jabadiagm/MSXgoauld_tn20k/fpga/OCM_3.9/peripheral/iplrom_304k.vhd

--
-- iplrom_304k.vhd
--   initial program loader for Cyclone & EPCS (Altera)
--   Revision 2.00
--
-- Copyright (c) 2006 Kazuhiro Tsujikawa (ESE Artists' factory)
-- All rights reserved.
--
-- Redistribution and use of this source code or any derivative works, are
-- permitted provided that the following conditions are met:
--
-- 1. Redistributions of source code must retain the above copyright notice,
--    this list of conditions and the following disclaimer.
-- 2. Redistributions in binary form must reproduce the above copyright
--    notice, this list of conditions and the following disclaimer in the
--    documentation and/or other materials provided with the distribution.
-- 3. Redistributions may not be sold, nor may they be used in a commercial
--    product or activity without specific prior written permission.
--
-- THIS SOFTWARE IS PROVIDED BY THE COPYRIGHT HOLDERS AND CONTRIBUTORS
-- "AS IS" AND ANY EXPRESS OR IMPLIED WARRANTIES, INCLUDING, BUT NOT LIMITED
-- TO, THE IMPLIED WARRANTIES OF MERCHANTABILITY AND FITNESS FOR A PARTICULAR
-- PURPOSE ARE DISCLAIMED. IN NO EVENT SHALL THE COPYRIGHT OWNER OR
-- CONTRIBUTORS BE LIABLE FOR ANY DIRECT, INDIRECT, INCIDENTAL, SPECIAL,
-- EXEMPLARY, OR CONSEQUENTIAL DAMAGES (INCLUDING, BUT NOT LIMITED TO,
-- PROCUREMENT OF SUBSTITUTE GOODS OR SERVICES; LOSS OF USE, DATA, OR PROFITS;
-- OR BUSINESS INTERRUPTION) HOWEVER CAUSED AND ON ANY THEORY OF LIABILITY,
-- WHETHER IN CONTRACT, STRICT LIABILITY, OR TORT (INCLUDING NEGLIGENCE OR
-- OTHERWISE) ARISING IN ANY WAY OUT OF THE USE OF THIS SOFTWARE, EVEN IF
-- ADVISED OF THE POSSIBILITY OF SUCH DAMAGE.
--
-- IPL-ROM Revision 2.00 for 304 kB unpacked
-- EPCS4 start adr 34000h - Optimized by KdL 2017.09.18
--

library ieee;
    use ieee.std_logic_1164.all;
    use ieee.std_logic_unsigned.all;

entity iplrom is
    port (
        clk     : in  std_logic;
        adr     : in  std_logic_vector ( 15 downto 0 );
        dbi     : out std_logic_vector (  7 downto 0 )
    );
end iplrom;

architecture rtl of iplrom is
    type rom_type is array ( 0 to 763 + 260 ) of std_logic_vector (  7 downto 0 );
    constant ipl_data : rom_type := (
        X"F3",X"01",X"FC",X"02",X"11",X"00",X"FC",X"63",X"6B",X"ED",X"B0",X"21",X"4C",X"FD",X"01",X"99",
        X"02",X"ED",X"B3",X"01",X"9A",X"20",X"ED",X"BB",X"C3",X"1B",X"FC",X"31",X"FF",X"FF",X"3E",X"D4",
        X"D3",X"40",X"3E",X"80",X"32",X"00",X"70",X"2A",X"00",X"80",X"11",X"41",X"42",X"ED",X"52",X"CA",
        X"1D",X"FD",X"3E",X"40",X"32",X"00",X"60",X"21",X"00",X"C0",X"04",X"4D",X"55",X"5D",

--      X"C3",X"86",X"FC",X"38",X"43",      -- loading BIOS from EPCS only
        X"CD",X"14",X"FE",X"38",X"43",      -- loading BIOS from SD CARD or EPCS (default)
--      X"CD",X"14",X"FE",X"38",X"FB",      -- loading BIOS from SD CARD only

                          X"21",X"00",X"C0",X"01",X"80",X"00",X"3E",X"46",X"ED",X"B1",X"B7",X"20",X"0C",
        X"86",X"23",X"86",X"D6",X"DB",X"2B",X"20",X"F1",X"48",X"59",X"51",X"37",X"38",X"57",X"06",X"04",
        X"21",X"C6",X"C1",X"E5",X"5E",X"23",X"56",X"23",X"4E",X"79",X"B2",X"B3",X"E1",X"20",X"07",X"11",
        X"10",X"00",X"19",X"10",X"EE",X"37",X"38",X"0E",X"D5",X"C5",X"06",X"01",X"21",X"00",X"C0",X"CD",
        X"14",X"FE",X"C1",X"D1",X"30",X"2F",X"21",X"8C",X"FD",X"22",X"7E",X"FD",X"3E",X"60",X"32",X"00",
        X"60",X"11",X"A0",X"01",X"3E",X"80",X"06",X"03",X"CD",X"6C",X"FD",X"06",X"03",X"CD",X"66",X"FD",
        X"CD",X"6C",X"FD",X"CD",X"4F",X"FD",X"06",X"05",X"CD",X"6C",X"FD",X"CD",X"61",X"FD",X"06",X"07",
        X"CD",X"6C",X"FD",X"18",X"66",X"DD",X"21",X"00",X"C0",X"DD",X"6E",X"0E",X"DD",X"66",X"0F",X"79",
        X"19",X"CE",X"00",X"4F",X"DD",X"5E",X"11",X"DD",X"56",X"12",X"7B",X"E6",X"0F",X"06",X"04",X"CB",
        X"3A",X"CB",X"1B",X"10",X"FA",X"B7",X"28",X"01",X"13",X"D5",X"DD",X"46",X"10",X"DD",X"5E",X"16",
        X"DD",X"56",X"17",X"79",X"19",X"CE",X"00",X"10",X"FB",X"D1",X"19",X"EB",X"4F",X"D5",X"C5",X"06",
        X"01",X"21",X"00",X"C0",X"CD",X"14",X"FE",X"38",X"0E",X"2A",X"00",X"C0",X"11",X"41",X"42",X"B7",
        X"ED",X"52",X"C1",X"D1",X"28",X"01",X"37",X"DA",X"86",X"FC",X"3E",X"80",X"06",X"09",X"CD",X"6E",
        X"FD",X"CD",X"4F",X"FD",X"06",

--      X"0F",                              -- loading BIOS 384 kB from SD CARD / JIS1 only
        X"17",                              -- loading BIOS 512 kB from SD CARD / JIS1+JIS2 (default)

                                            X"CD",X"6E",X"FD",X"2F",X"07",X"D3",X"4E",X"AF",X"32",X"00",
        X"60",X"3C",X"32",X"00",X"68",X"32",X"00",X"70",X"32",X"00",X"78",X"3E",X"C0",X"D3",X"A8",X"C7",
        X"77",X"05",X"55",X"02",X"65",X"04",X"11",X"06",X"64",X"06",X"61",X"03",X"73",X"01",X"71",X"06",
        X"27",X"01",X"51",X"03",X"27",X"01",X"17",X"07",X"33",X"06",X"11",X"00",X"00",X"90",X"00",X"08",
        X"3A",X"2D",X"80",X"D6",X"03",X"D3",X"4F",X"D3",X"F4",X"0F",X"F6",X"C9",X"32",X"BB",X"FD",X"08",
        X"C9",X"21",X"18",X"23",X"18",X"03",X"21",X"18",X"25",X"22",X"95",X"FD",X"4B",X"04",X"32",X"00",
        X"70",X"3C",X"32",X"00",X"78",X"3C",X"F5",X"C5",X"06",X"20",X"21",X"00",X"80",X"CD",X"14",X"FE",
        X"C1",X"E1",X"D8",X"7C",X"10",X"E8",X"60",X"68",X"22",X"95",X"FD",X"C9",X"D5",X"C5",X"CB",X"23",
        X"CB",X"12",X"48",X"AF",X"47",X"00",X"00",X"E5",X"21",X"00",X"40",X"36",X"03",X"72",X"73",X"70",
        X"7E",X"D1",X"7E",X"12",X"13",X"7E",X"12",X"13",X"10",X"F8",X"0D",X"20",X"F5",X"3A",X"00",X"50",
        X"C1",X"E1",X"AF",X"57",X"58",X"19",X"EB",X"89",X"4F",X"C9",X"3E",X"FF",X"EB",X"12",X"13",X"12",
        X"13",X"10",X"FA",X"0D",X"20",X"F7",X"C1",X"D1",X"AF",X"18",X"EC",X"3A",X"CF",X"FF",X"FE",X"03",
        X"28",X"06",X"FE",X"02",X"28",X"0D",X"37",X"C9",X"7E",X"70",X"36",X"00",X"71",X"72",X"73",X"36",
        X"95",X"18",X"1A",X"CB",X"23",X"CB",X"12",X"CB",X"11",X"7E",X"70",X"71",X"72",X"73",X"36",X"00",
        X"36",X"95",X"18",X"09",X"7E",X"70",X"36",X"00",X"36",X"00",X"71",X"72",X"73",X"7E",X"01",X"10",
        X"00",X"7E",X"FE",X"FF",X"3F",X"D0",X"0B",X"78",X"B1",X"20",X"F6",X"37",X"C9",X"CD",X"45",X"FE",
        X"C1",X"D1",X"E1",X"D8",X"E5",X"D5",X"C5",X"06",X"51",X"21",X"00",X"40",X"CD",X"CB",X"FD",X"38",
        X"EC",X"C1",X"D1",X"E1",X"B7",X"37",X"C0",X"D5",X"C5",X"EB",X"01",X"00",X"02",X"21",X"00",X"40",
        X"7E",X"FE",X"FE",X"20",X"FB",X"ED",X"B0",X"EB",X"1A",X"C1",X"1A",X"D1",X"13",X"7A",X"B3",X"20",
        X"01",X"0C",X"10",X"D0",X"C9",X"CD",X"5A",X"FE",X"D8",X"C0",X"21",X"CF",X"FF",X"3E",X"03",X"BB",
        X"20",X"04",X"36",X"03",X"18",X"02",X"36",X"02",X"AF",X"C9",X"21",X"00",X"40",X"06",X"0A",X"3A",
        X"00",X"50",X"10",X"FB",X"01",X"00",X"40",X"11",X"00",X"00",X"CD",X"E9",X"FD",X"D8",X"E6",X"F3",
        X"FE",X"01",X"C0",X"01",X"01",X"48",X"11",X"87",X"AA",X"CD",X"F4",X"FD",X"D8",X"FE",X"01",X"20",
        X"42",X"7E",X"00",X"7E",X"00",X"7E",X"E6",X"0F",X"FE",X"01",X"C0",X"7E",X"FE",X"AA",X"C0",X"01",
        X"00",X"77",X"11",X"00",X"00",X"CD",X"E9",X"FD",X"D8",X"FE",X"01",X"C0",X"01",X"40",X"69",X"11",
        X"00",X"00",X"CD",X"E9",X"FD",X"D8",X"E6",X"01",X"FE",X"01",X"28",X"E3",X"01",X"00",X"7A",X"11",
        X"00",X"00",X"CD",X"E9",X"FD",X"D8",X"7E",X"BE",X"BE",X"BE",X"CB",X"77",X"1E",X"02",X"28",X"01",
        X"1C",X"AF",X"C9",X"01",X"00",X"77",X"11",X"00",X"00",X"CD",X"E9",X"FD",X"D8",X"CB",X"57",X"20",
        X"19",X"FE",X"01",X"C0",X"01",X"00",X"69",X"11",X"00",X"00",X"CD",X"E9",X"FD",X"D8",X"CB",X"57",
        X"20",X"08",X"CB",X"47",X"20",X"DD",X"AF",X"1E",X"01",X"C9",X"01",X"00",X"41",X"11",X"00",X"00",
        X"CD",X"E9",X"FD",X"D8",X"FE",X"01",X"28",X"CB",X"1E",X"00",X"B7",X"C9",

        -- a lot of $FF to reduce LEs (optimization trick)
                                                                                X"FF",X"FF",X"FF",X"FF",    -- 00
        X"FF",X"FF",X"FF",X"FF",X"FF",X"FF",X"FF",X"FF",X"FF",X"FF",X"FF",X"FF",X"FF",X"FF",X"FF",X"FF",    -- 01
        X"FF",X"FF",X"FF",X"FF",X"FF",X"FF",X"FF",X"FF",X"FF",X"FF",X"FF",X"FF",X"FF",X"FF",X"FF",X"FF",    -- 02
        X"FF",X"FF",X"FF",X"FF",X"FF",X"FF",X"FF",X"FF",X"FF",X"FF",X"FF",X"FF",X"FF",X"FF",X"FF",X"FF",    -- 03
        X"FF",X"FF",X"FF",X"FF",X"FF",X"FF",X"FF",X"FF",X"FF",X"FF",X"FF",X"FF",X"FF",X"FF",X"FF",X"FF",    -- 04
        X"FF",X"FF",X"FF",X"FF",X"FF",X"FF",X"FF",X"FF",X"FF",X"FF",X"FF",X"FF",X"FF",X"FF",X"FF",X"FF",    -- 05
        X"FF",X"FF",X"FF",X"FF",X"FF",X"FF",X"FF",X"FF",X"FF",X"FF",X"FF",X"FF",X"FF",X"FF",X"FF",X"FF",    -- 06
        X"FF",X"FF",X"FF",X"FF",X"FF",X"FF",X"FF",X"FF",X"FF",X"FF",X"FF",X"FF",X"FF",X"FF",X"FF",X"FF",    -- 07
        X"FF",X"FF",X"FF",X"FF",X"FF",X"FF",X"FF",X"FF",X"FF",X"FF",X"FF",X"FF",X"FF",X"FF",X"FF",X"FF",    -- 08
        X"FF",X"FF",X"FF",X"FF",X"FF",X"FF",X"FF",X"FF",X"FF",X"FF",X"FF",X"FF",X"FF",X"FF",X"FF",X"FF",    -- 09
        X"FF",X"FF",X"FF",X"FF",X"FF",X"FF",X"FF",X"FF",X"FF",X"FF",X"FF",X"FF",X"FF",X"FF",X"FF",X"FF",    -- 10
        X"FF",X"FF",X"FF",X"FF",X"FF",X"FF",X"FF",X"FF",X"FF",X"FF",X"FF",X"FF",X"FF",X"FF",X"FF",X"FF",    -- 11
        X"FF",X"FF",X"FF",X"FF",X"FF",X"FF",X"FF",X"FF",X"FF",X"FF",X"FF",X"FF",X"FF",X"FF",X"FF",X"FF",    -- 12
        X"FF",X"FF",X"FF",X"FF",X"FF",X"FF",X"FF",X"FF",X"FF",X"FF",X"FF",X"FF",X"FF",X"FF",X"FF",X"FF",    -- 13
        X"FF",X"FF",X"FF",X"FF",X"FF",X"FF",X"FF",X"FF",X"FF",X"FF",X"FF",X"FF",X"FF",X"FF",X"FF",X"FF",    -- 14
        X"FF",X"FF",X"FF",X"FF",X"FF",X"FF",X"FF",X"FF",X"FF",X"FF",X"FF",X"FF",X"FF",X"FF",X"FF",X"FF",    -- 15
        X"FF",X"FF",X"FF",X"FF",X"FF",X"FF",X"FF",X"FF",X"FF",X"FF",X"FF",X"FF",X"FF",X"FF",X"FF",X"FF"     -- 16
    );

begin

    process( clk )
    begin
        if( clk'event and clk = '1' )then
            dbi <= ipl_data( conv_integer( adr(  9 downto 0 )));    -- conv_integer is limited to 1024 bytes
        end if;
    end process;

end rtl;
