jabadiagm/MSXgoauld_tn20k/fpga/OCM_3.9/peripheral/wifi.vhd

--
-- wifi.vhd
--   Wi-Fi to Serial Module ESP2866 and UART to interface with it (for XTAL 21.47727MHz)
--   Revision 1.05
--
-- 1.01 - Fixed reading of 06 and 07 not returning the real data but the previous latched data.
--      - Fixed received 06 command not being executed until a next command was received.
-- 1.02 - Added possibility of activating interrupts (CMD 21) and deactivating it (CMD 22).
--        Default is off as if no one services the interrupt, it won't clear and z80 will
--        lock executing the interrupt routine executed until a next command was received.
-- 1.03 - Changed Available Baud Rate List, adding 859372 BPS as 0 (maximum), 346520 BPS as 1
--        and 230400 as 2, removed 2400bps options. Removed interrupt support, not needed for
--        UNAPI ESP firmware, so let's not waste cells and use them for other hardware! :-)
-- 1.04 - Quick Receive support: interface will wait up to 25ms for a byte to come in the
--        UART if a request has been made and no data still is available. This allows the
--        receiving routines to be faster, as once they know they will to receive a lot of
--        data, there is no need to keep polling the status for every byte. In the rare case
--        no data comes within 25ms (for a well programmed driver, that is :-)), a status bit
--        will be set warning about buffer underrun, so that driver can retry receiving the
--        last response.
-- 1.05 - Quick Receive optimized with LFSR counter.
--
-- Copyright (c) 2019-2021 Oduvaldo Pavan Junior ( ducasp@ gmail.com )
-- Based on Victor Trucco Spectrum Next Wi-Fi interface
-- All rights reserved.
--
-- Redistribution and use of this source code or any derivative works, are
-- permitted provided that the following conditions are met:
--
-- 1. Redistributions of source code must retain the above copyright notice,
--    this list of conditions and the following disclaimer.
-- 2. Redistributions in binary form must reproduce the above copyright
--    notice, this list of conditions and the following disclaimer in the
--    documentation and/or other materials provided with the distribution.
-- 3. Redistributions may not be sold, nor may they be used in a commercial
--    product or activity without specific prior written permission.
--
-- THIS SOFTWARE IS PROVIDED BY THE COPYRIGHT HOLDERS AND CONTRIBUTORS
-- "AS IS" AND ANY EXPRESS OR IMPLIED WARRANTIES, INCLUDING, BUT NOT LIMITED
-- TO, THE IMPLIED WARRANTIES OF MERCHANTABILITY AND FITNESS FOR A PARTICULAR
-- PURPOSE ARE DISCLAIMED. IN NO EVENT SHALL THE COPYRIGHT OWNER OR
-- CONTRIBUTORS BE LIABLE FOR ANY DIRECT, INDIRECT, INCIDENTAL, SPECIAL,
-- EXEMPLARY, OR CONSEQUENTIAL DAMAGES (INCLUDING, BUT NOT LIMITED TO,
-- PROCUREMENT OF SUBSTITUTE GOODS OR SERVICES; LOSS OF USE, DATA, OR PROFITS;
-- OR BUSINESS INTERRUPTION) HOWEVER CAUSED AND ON ANY THEORY OF LIABILITY,
-- WHETHER IN CONTRACT, STRICT LIABILITY, OR TORT (INCLUDING NEGLIGENCE OR
-- OTHERWISE) ARISING IN ANY WAY OUT OF THE USE OF THIS SOFTWARE, EVEN IF
-- ADVISED OF THE POSSIBILITY OF SUCH DAMAGE.
--
-- Address 0x07 send to tx uart buffer or read to get uart status
--
-- Address 0x06 send to set UART speed or read to get uart rx buffer
--
-- 0x06 Address Write commands:
--
-- 0 - UART 859372 bps
-- 1 - UART 346520 bps
-- 2 - UART 231014 bps
-- 3 - UART 115200 bps
-- 4 - UART 57600 bps
-- 5 - UART 38400 bps
-- 6 - UART 31250 bps
-- 7 - UART 19200 bps
-- 8 - UART 9600 bps
-- 9 - UART 4800 bps
-- 20 - Clear FIFO buffer
--
-- 0x07 Address Uart Status bits:
--
-- bit 0 - does fifo rx buffer have data?
-- bit 1 - is data transmission in progress?
-- bit 2 - is fifo rx buffer full?
-- bit 3 - does the interface support quick receive?
-- bit 4 - did buffer underrun occur? Reset automatically once read
-- bit 6 - 0 if in interrupt with 128 bytes of data or more, 1 if free (avoid open bus confusion)
-- bit 7 - 0 if in interrupt, 1 if free (avoid open bus confusion)
--
-- Quick Receive:
-- Quick Receive hold on the adapter the responsibility to wait a little bit if a read has been issued
-- and no data has been received. Basically what it does is, every time someone try to read from UART
-- and no counter has been setup, it will wait up to the equivalent of 25ms to receive characters since
-- the first read request. The counter is reset everytime a a transmission is made. As the ESP is a
-- slave device, that works quite nice for us
--

library ieee;
    use ieee.std_logic_1164.all;
    use ieee.std_logic_unsigned.all;
    use ieee.numeric_std.ALL;

entity wifi is
    port(
        clk_i       : in    std_logic;
        wait_o      : out   std_logic := '1';
        reset_i     : in    std_logic;
        iorq_i      : in    std_logic;
        wrt_i       : in    std_logic;
        rd_i        : in    std_logic;
        tx_i        : in    std_logic;
        rx_o        : out   std_logic;
        adr_i       : in    std_logic_vector( 15 downto 0 );
        db_i        : in    std_logic_vector(  7 downto 0 );
        db_o        : out   std_logic_vector(  7 downto 0 ) := (others => 'Z')
    );
end wifi;
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
